SphaeroX/esp32_plant_scale/include/cred.h

#ifndef CRED_H
#define CRED_H

// WLAN Zugangsdaten
extern const char *ssid;     // WLAN-Name
extern const char *password; // WLAN-Passwort

// ThingSpeak Einstellungen
extern unsigned long channelID; // Deine Channel ID
extern const char *apiKey;      // Dein Write API Key

#endif
